hselomein/Car-LED-Controller/CAD/Corey's Rear Enclosure2-Body.stl

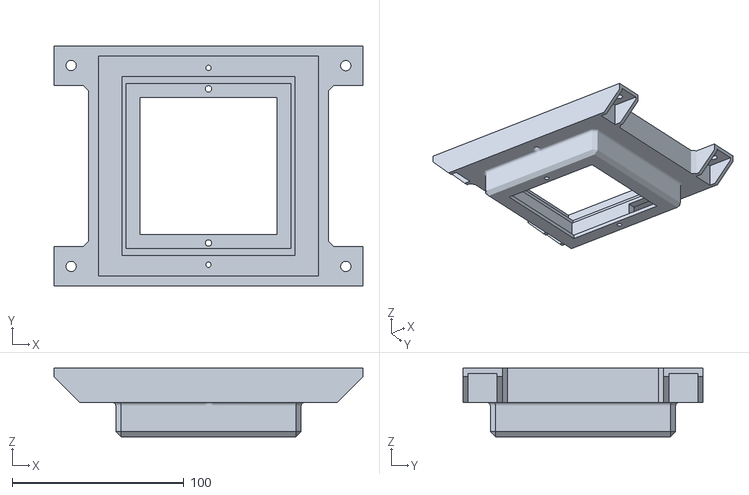
[picture p24: CAD file, 2023-12-11]
CAD/Corey's Rear Enclosure2-Body.stl
180.0 x 140.0 x 40.0
