hselomein/Car-LED-Controller/CAD/Corey's Rear Enclosure2-Door.stl

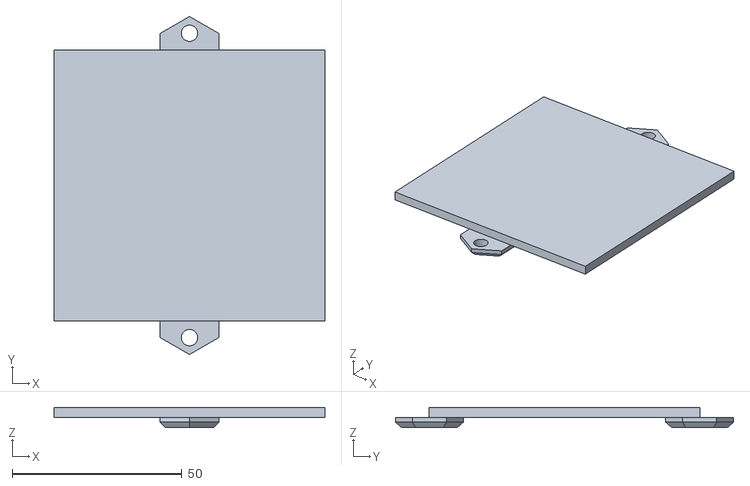
[picture p25: CAD file, 2023-12-05]
CAD/Corey's Rear Enclosure2-Door.stl
79.8 x 99.7 x 6.00
