hselomein/Car-LED-Controller/CAD/Corey's Rear Enclosure-Lid.stl

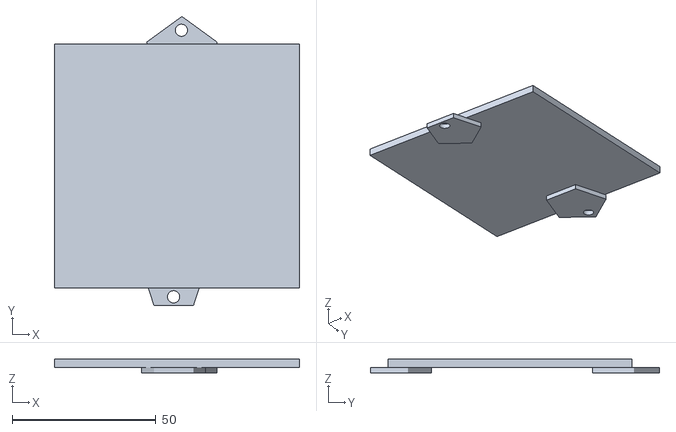
[picture p26: CAD file, 2023-11-26]
CAD/Corey's Rear Enclosure-Lid.stl
85.1 x 100.4 x 5.00
