hselomein/Car-LED-Controller/CAD/GreenyBig.step

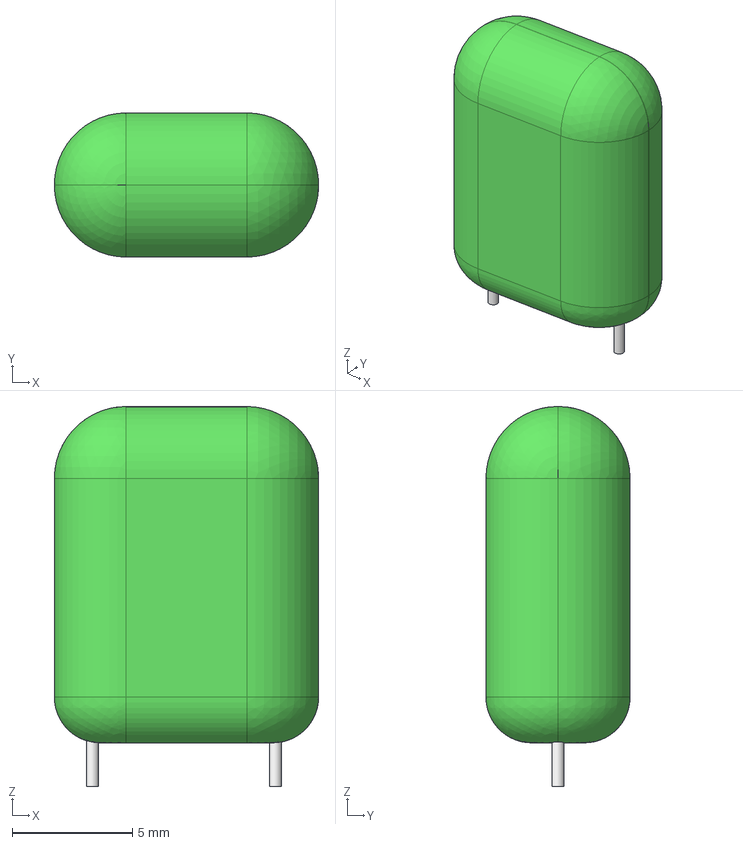
[picture p27: CAD file, 2023-11-26]
CAD/GreenyBig.step
11.0 x 6.00 x 15.8 mm
