hselomein/Car-LED-Controller/CAD/Corey's Rear Enclosure-Body.stl

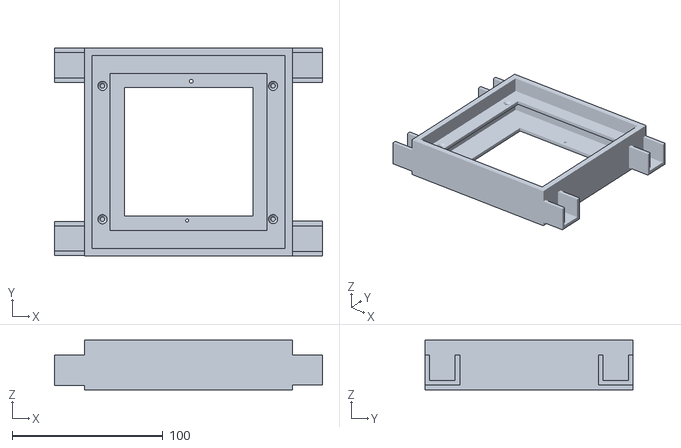
[picture p28: CAD file, 2023-11-26]
CAD/Corey's Rear Enclosure-Body.stl
178.0 x 138.0 x 33.0
