hselomein/Car-LED-Controller/CAD/Corey's Rear Enclosure.FCStd

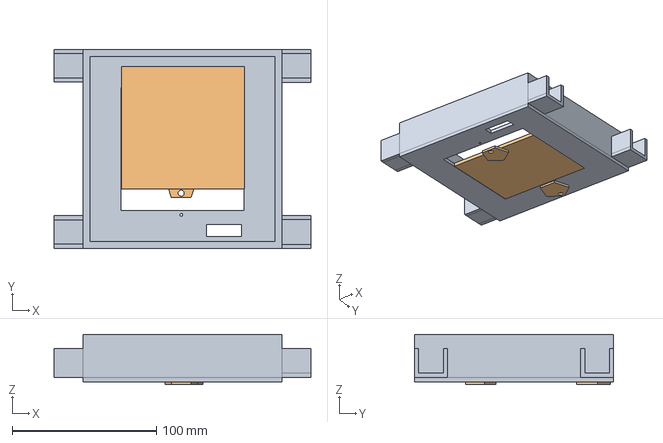
[picture p29: CAD file, 2023-11-26]
CAD/Corey's Rear Enclosure.FCStd
178.0 x 138.0 x 34.9 mm
Lid
