hselomein/Car-LED-Controller/CAD/GreenyMedium.step

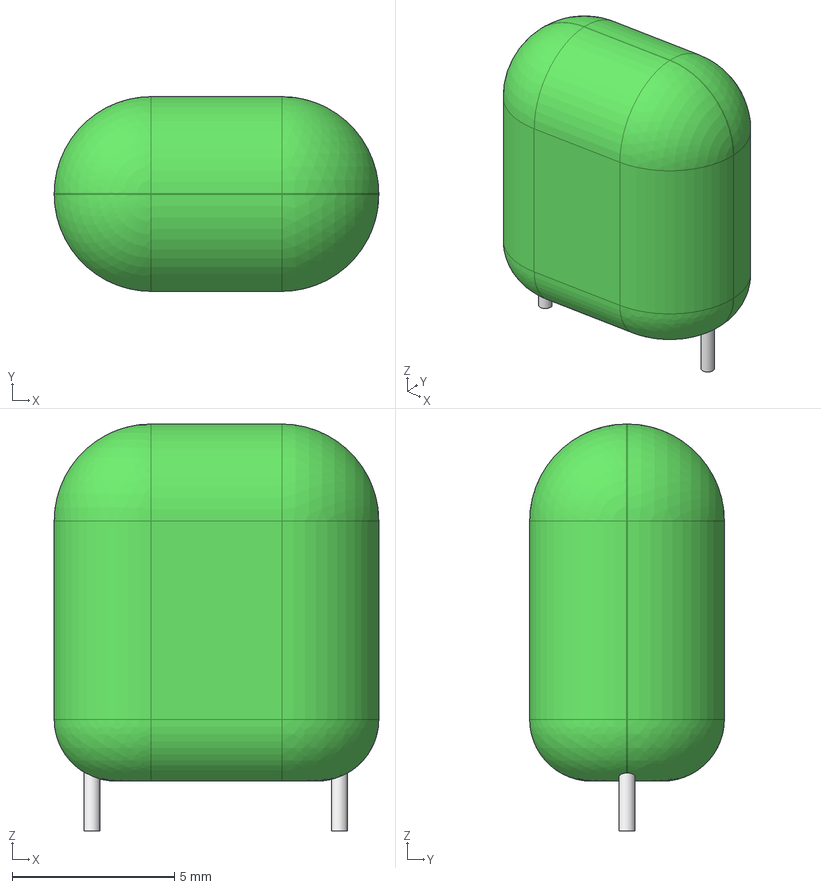
[picture p30: CAD file, 2023-11-26]
CAD/GreenyMedium.step
10.0 x 6.00 x 12.5 mm
