hselomein/Car-LED-Controller/CAD/Corey's Rear Enclosure.20231113-090606.FCStd

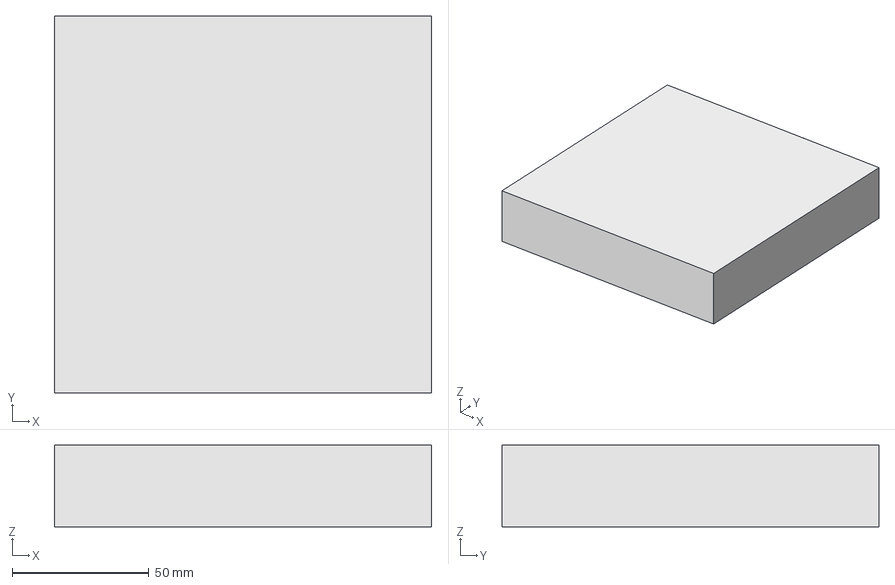
[picture p31: CAD file, 2023-11-26]
CAD/Corey's Rear Enclosure.20231113-090606.FCStd
138.0 x 138.0 x 30.0 mm
