hselomein/Car-LED-Controller/CAD/Controller Enclosure v1-64x64 LED Matrix.stl

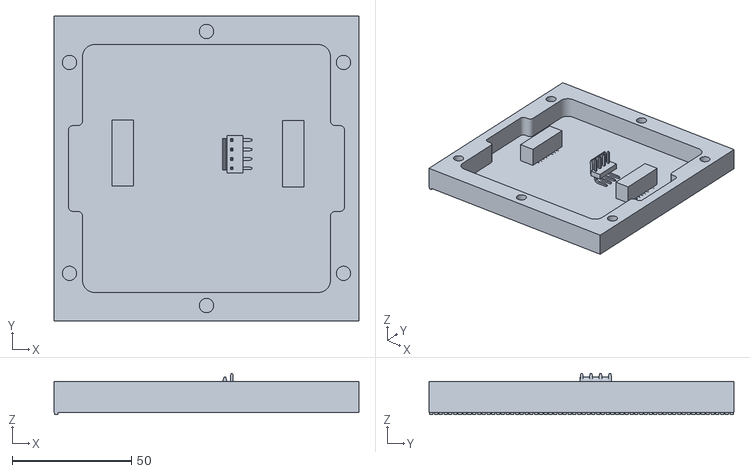
[picture p32: CAD file, 2023-11-26]
CAD/Controller Enclosure v1-64x64 LED Matrix.stl
128.0 x 128.0 x 17.4
