hselomein/Car-LED-Controller/CAD/GreenySmall.step

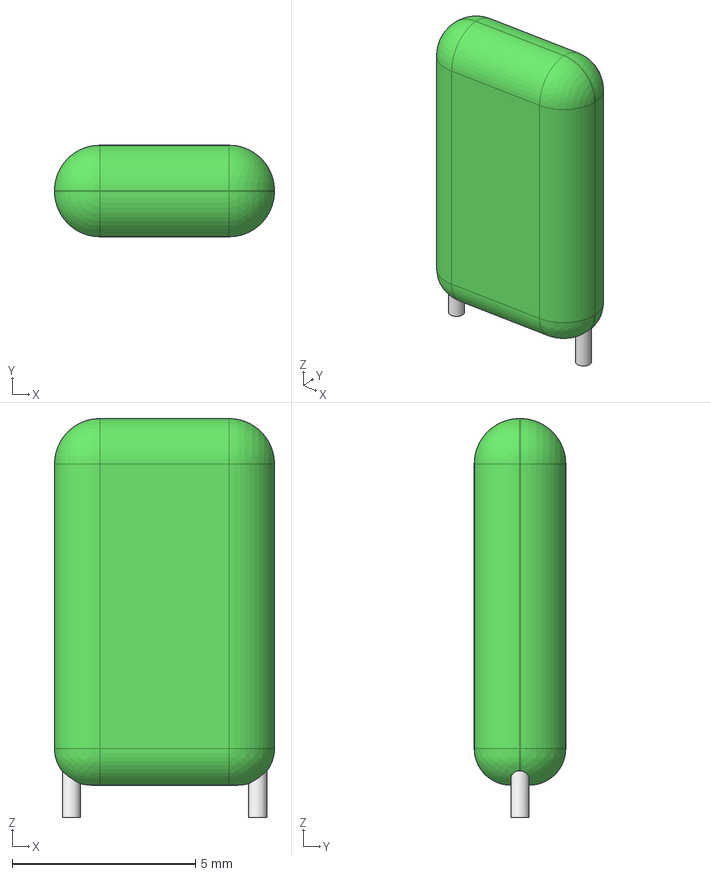
[picture p33: CAD file, 2023-11-26]
CAD/GreenySmall.step
6.00 x 2.50 x 10.9 mm
