hselomein/Car-LED-Controller/CAD/HTST-108-01-L-DV.stp

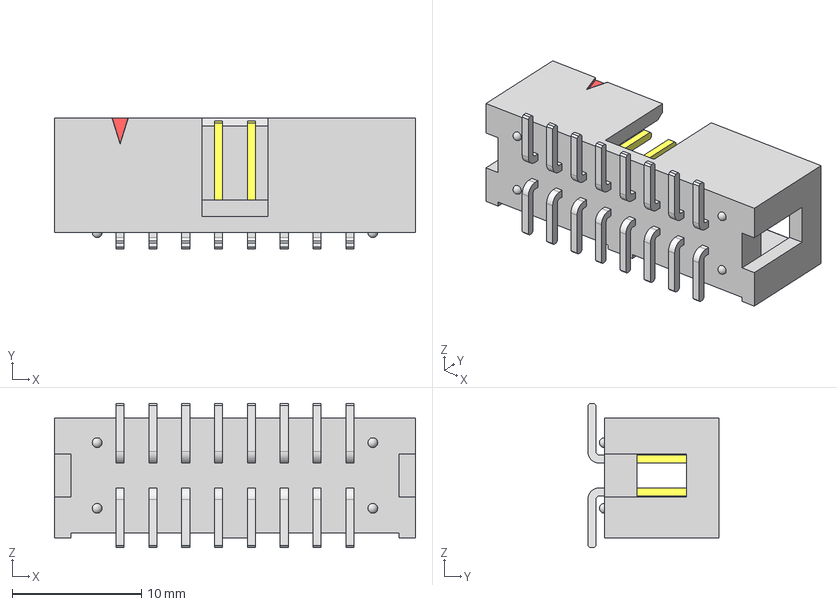
[picture p34: CAD file, 2023-10-11]
CAD/HTST-108-01-L-DV.stp
27.9 x 10.2 x 11.2 mm
T-1S6-08-01-DV-L2_
T-1S6-08-01-DV-L_
HTST-First_Position_Indicator
HTST-108-01-DV_header
