hselomein/Car-LED-Controller/CAD/TSS-113-01-L-D.stp

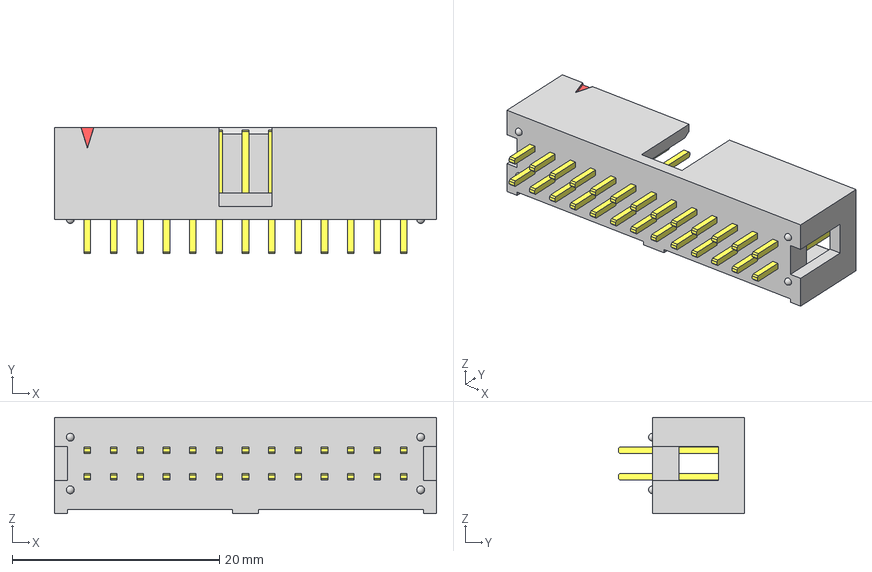
[picture p35: CAD file, 2023-10-11]
CAD/TSS-113-01-L-D.stp
36.8 x 12.2 x 9.27 mm
T-1S6-13-01-D__
TSS-First_Position_Indicator
TSS-113-01-D_header
