hselomein/Car-LED-Controller/CAD/female_header_a-bl254-eg-g19d.stp

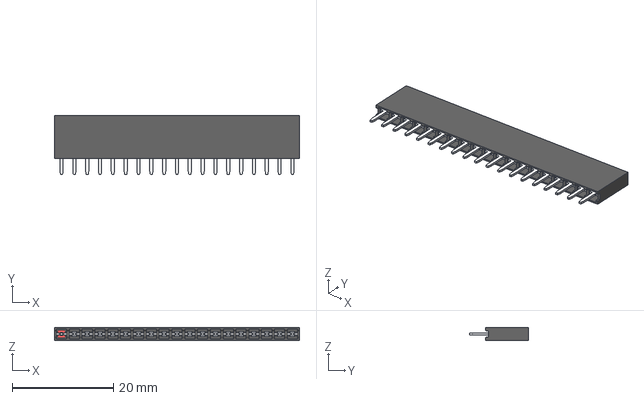
[picture p36: CAD file, 2023-08-22]
CAD/female_header_a-bl254-eg-g19d.stp
48.5 x 11.7 x 2.50 mm
