hselomein/Car-LED-Controller/CAD/female_header_a-bl254-eg-g06d.stp

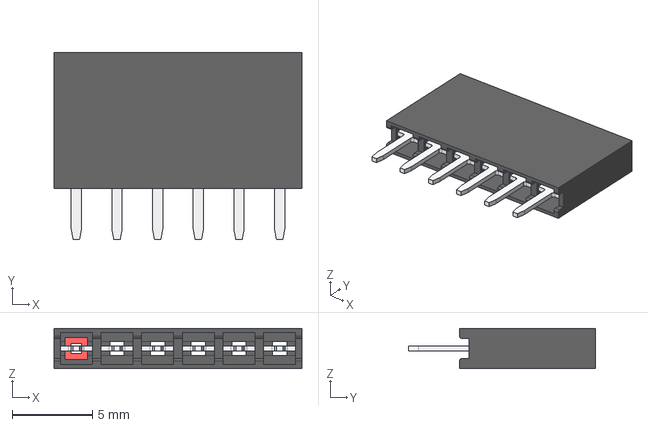
[picture p37: CAD file, 2023-08-22]
CAD/female_header_a-bl254-eg-g06d.stp
15.5 x 11.7 x 2.50 mm
