hselomein/Car-LED-Controller/CAD/pin_header_aw140-eg-g06d.stp

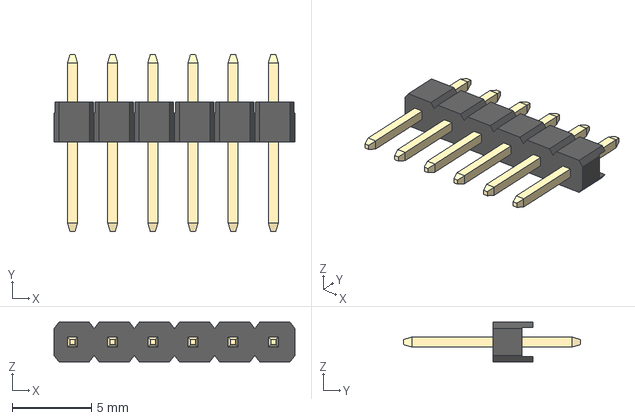
[picture p38: CAD file, 2023-08-22]
CAD/pin_header_aw140-eg-g06d.stp
15.2 x 11.2 x 2.50 mm
