hselomein/Car-LED-Controller/CAD/female_header_a-bl254-eg-g02d.stp

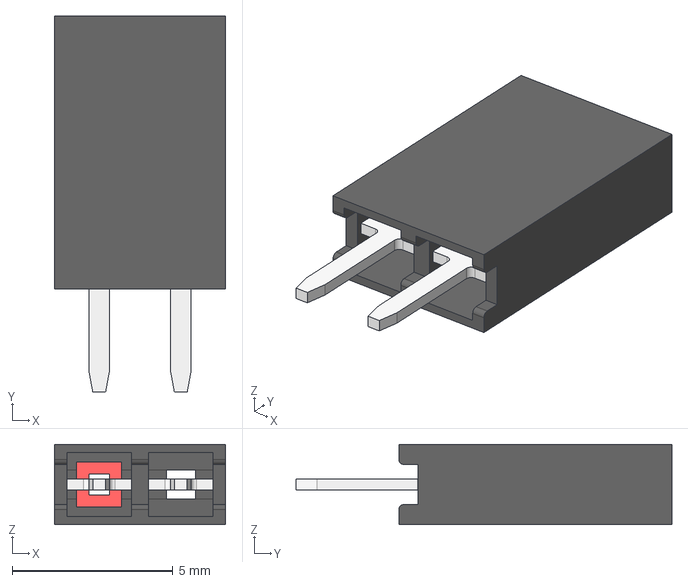
[picture p39: CAD file, 2023-08-22]
CAD/female_header_a-bl254-eg-g02d.stp
5.33 x 11.7 x 2.50 mm
