hselomein/Car-LED-Controller/CAD/Controller Enclosure v1.FCStd

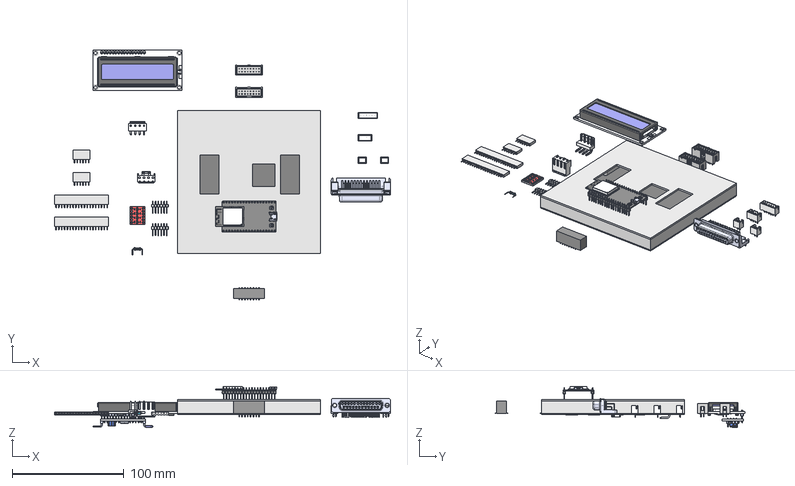
[picture p40: CAD file, 2023-08-22]
CAD/Controller Enclosure v1.FCStd
300.8 x 223.6 x 37.1 mm
Plastic Mount
PCB
board
board001
board002
board003
board004
board005
board006
board007
board008
board009
board010
board011
board012
board013
board014
board015
board016
board017
board018
board019
board020
board021
board022
board023
board024
board025
board026
board027
board028
board029
board030
board031
board032
board033
board034
board035
board036
board037
board038
header
header001
header002
header003
header004
header005
header006
header007
header008
header009
header010
header011
header012
header013
header014
header015
header016
header017
header018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
