hselomein/Car-LED-Controller/CAD/RES_AV_0.25W_100mil_0R_1%.STEP

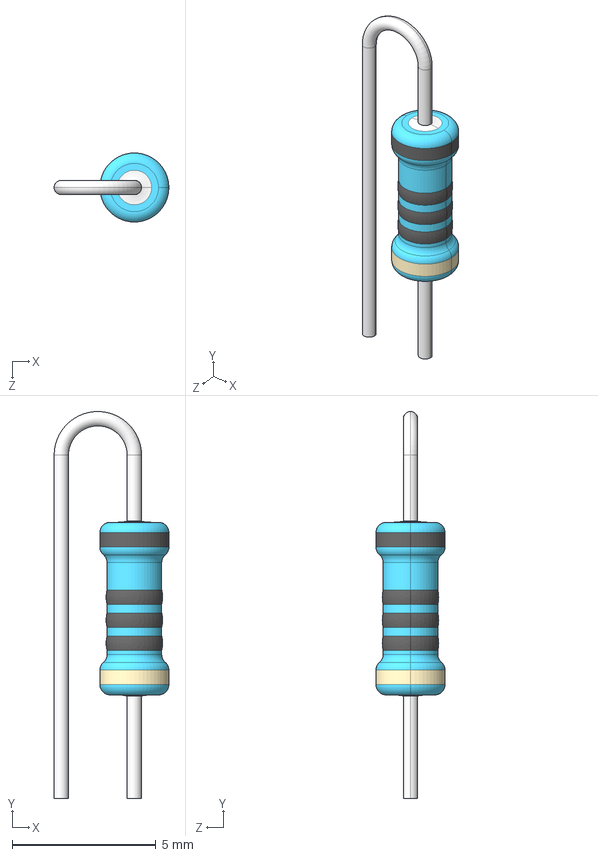
[picture p41: CAD file, 2023-08-22]
CAD/RES_AV_0.25W_100mil_0R_1%.STEP
3.99 x 13.5 x 2.40 mm
