hselomein/Car-LED-Controller/CAD/RES_AH_0.25W_500mil_0R_1%.STEP

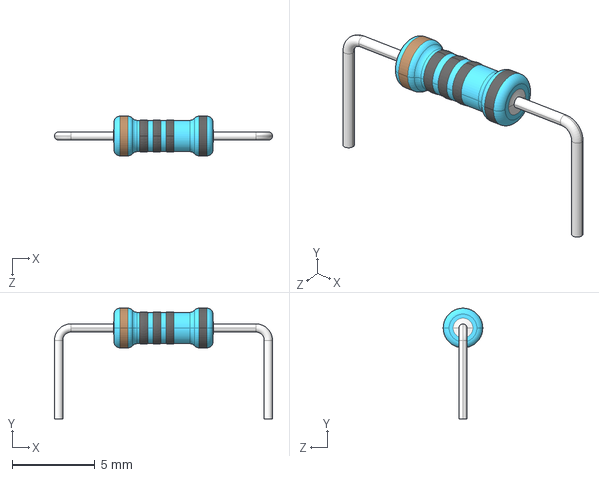
[picture p42: CAD file, 2023-08-22]
CAD/RES_AH_0.25W_500mil_0R_1%.STEP
13.2 x 6.70 x 2.40 mm
