hselomein/Car-LED-Controller/CAD/RES_AV_0.25W_200mil_0R_1%.STEP

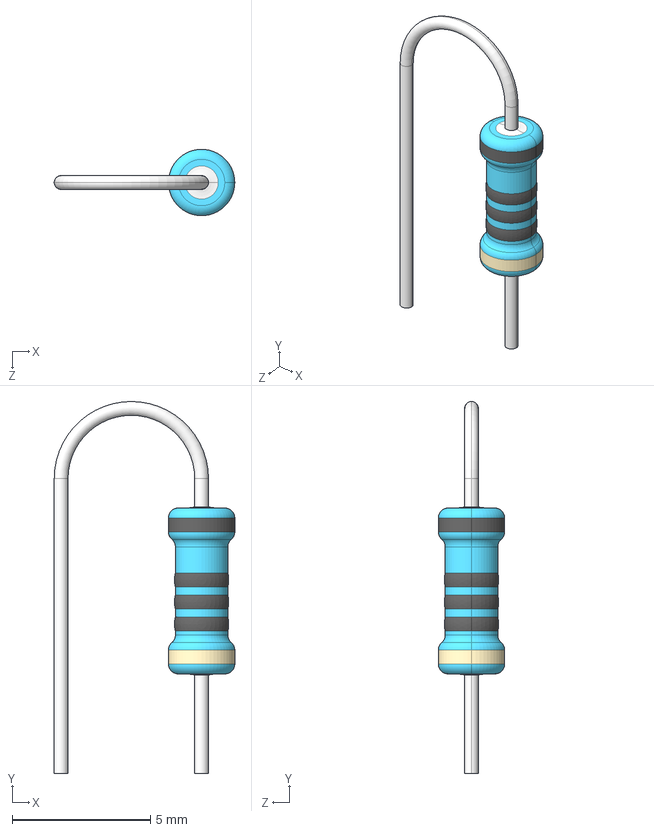
[picture p43: CAD file, 2023-08-22]
CAD/RES_AV_0.25W_200mil_0R_1%.STEP
6.53 x 13.5 x 2.40 mm
