hselomein/Car-LED-Controller/CAD/RES_AV_0.25W_150mil_0R_1%.STEP

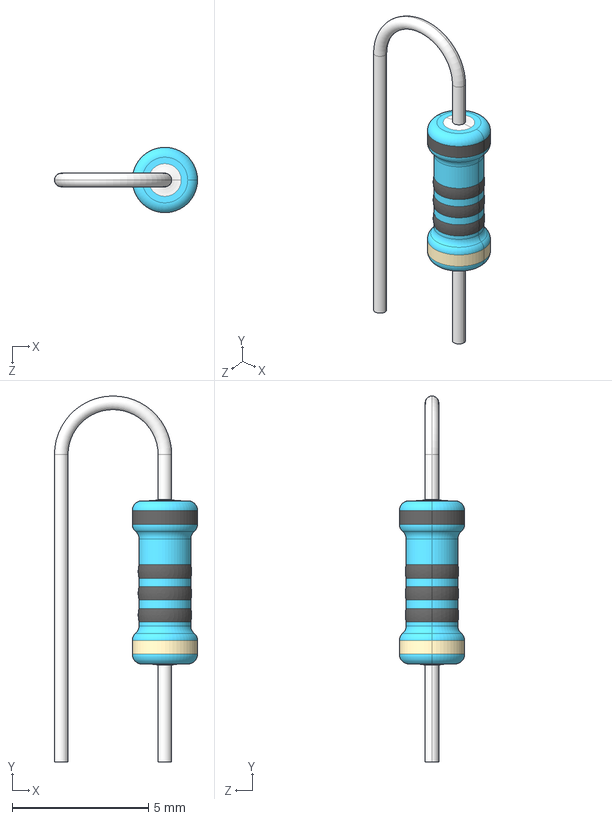
[picture p44: CAD file, 2023-08-22]
CAD/RES_AV_0.25W_150mil_0R_1%.STEP
5.26 x 13.4 x 2.40 mm
