hselomein/Car-LED-Controller/CAD/RES_AH_0.25W_600mil_0R_1%.STEP

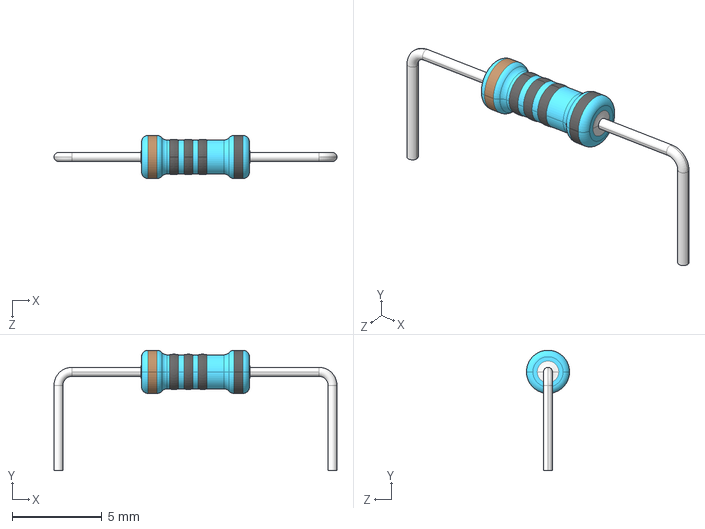
[picture p47: CAD file, 2023-08-22]
CAD/RES_AH_0.25W_600mil_0R_1%.STEP
15.7 x 6.70 x 2.40 mm
