hselomein/Car-LED-Controller/CAD/B4B-XH-A.step

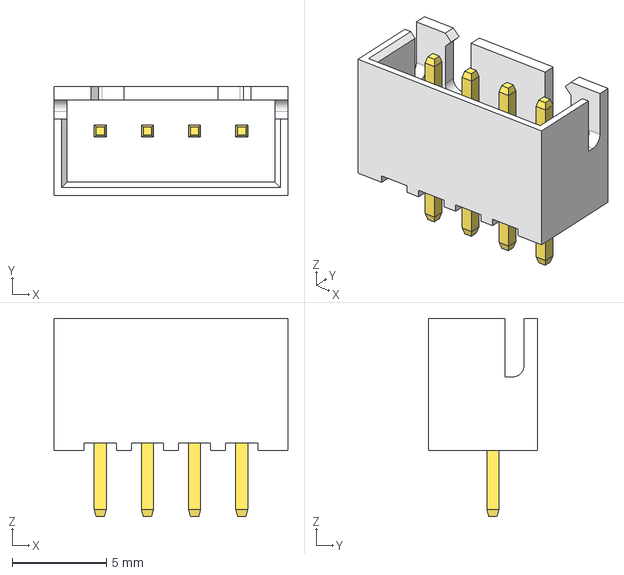
[picture p49: CAD file, 2023-08-22]
CAD/B4B-XH-A.step
12.4 x 5.75 x 10.5 mm
