hselomein/Car-LED-Controller/CAD/B6B-XH-A.step

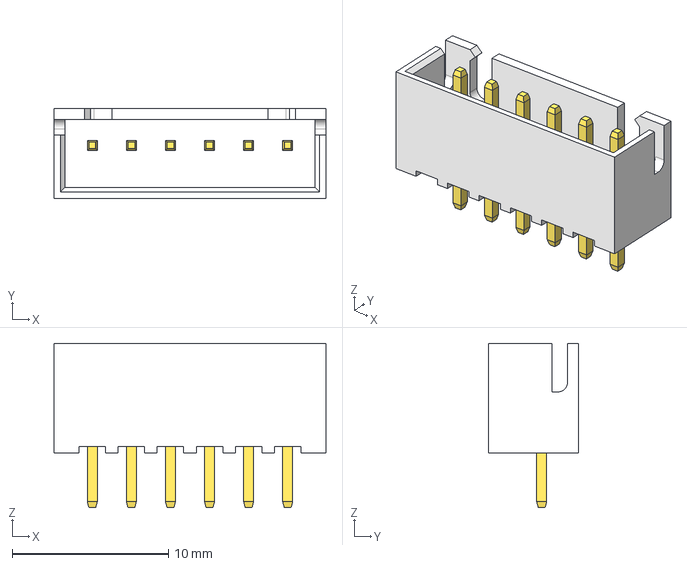
[picture p50: CAD file, 2023-08-22]
CAD/B6B-XH-A.step
17.4 x 5.75 x 10.5 mm
