hselomein/Car-LED-Controller/CAD/B2B-XH-A.step

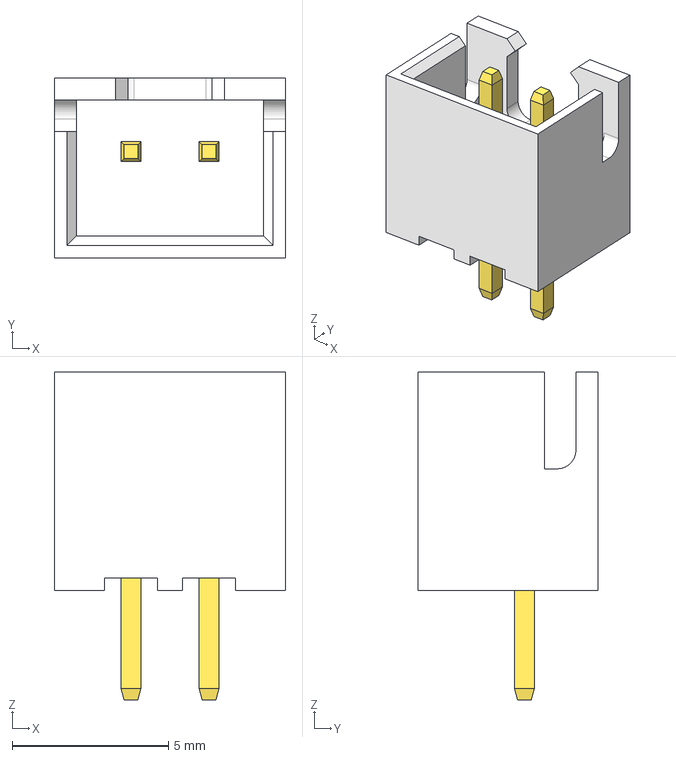
[picture p51: CAD file, 2023-08-22]
CAD/B2B-XH-A.step
7.40 x 5.75 x 10.5 mm
