hselomein/Car-LED-Controller/CAD/DB25S564GTLF--3DModel-STEP-56544.STEP

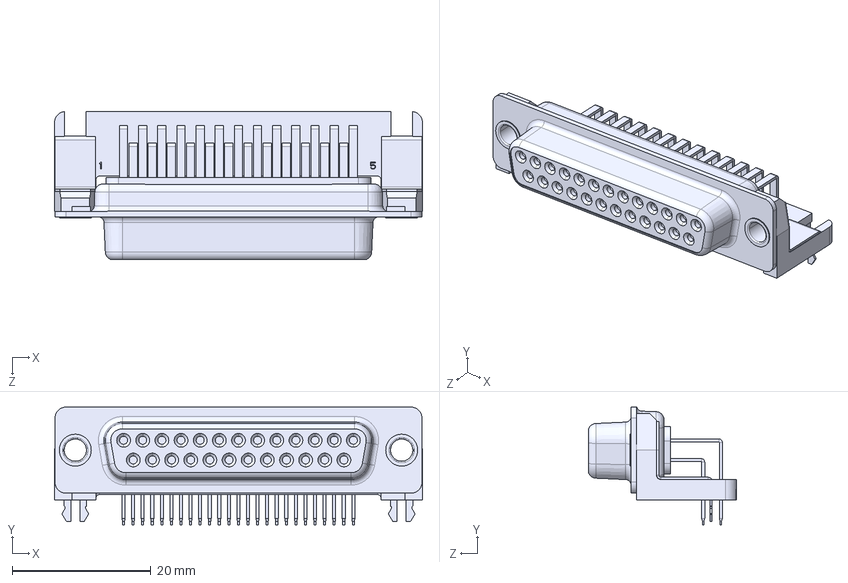
[picture p52: CAD file, 2023-08-21]
CAD/DB25S564GTLF--3DModel-STEP-56544.STEP
53.0 x 17.0 x 21.3 mm
