hselomein/Car-LED-Controller/CAD/SBH11-NBPC-D08-SM-BK.stp

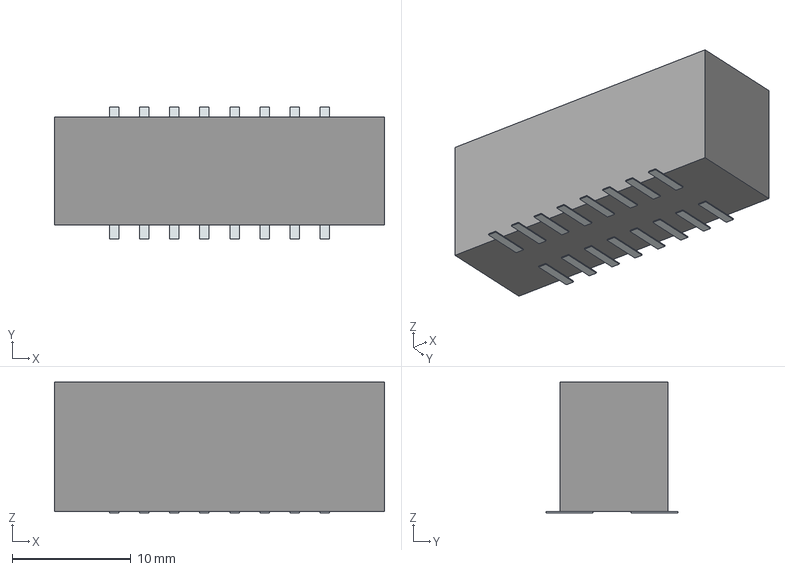
[picture p53: CAD file, 2023-08-21]
CAD/SBH11-NBPC-D08-SM-BK.stp
27.8 x 11.1 x 11.0 mm
Pins
