hselomein/Car-LED-Controller/CAD/TSS-108-01-G-D.stp

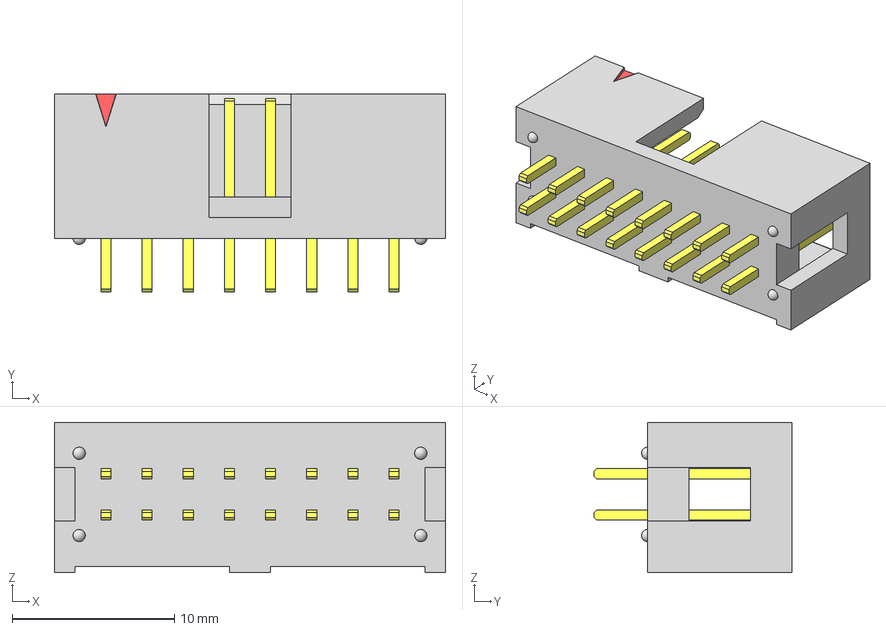
[picture p54: CAD file, 2023-08-21]
CAD/TSS-108-01-G-D.stp
24.1 x 12.2 x 9.27 mm
T-1S6-08-01-D__
TSS-First_Position_Indicator
TSS-108-01-D_header
