hselomein/Car-LED-Controller/CAD/User Library-VHR-4N.step

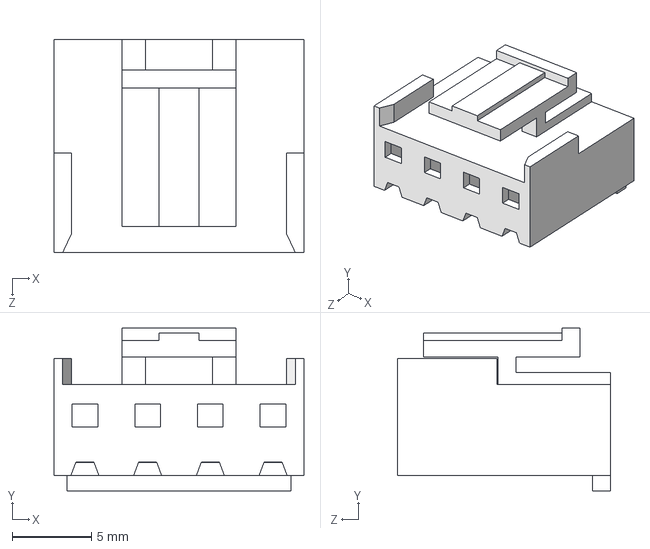
[picture p55: CAD file, 2023-08-21]
CAD/User Library-VHR-4N.step
15.8 x 10.3 x 13.5 mm
