hselomein/Car-LED-Controller/CAD/SFH11-PBPC-D08-ST-BK--3DModel-STEP-56544.STEP

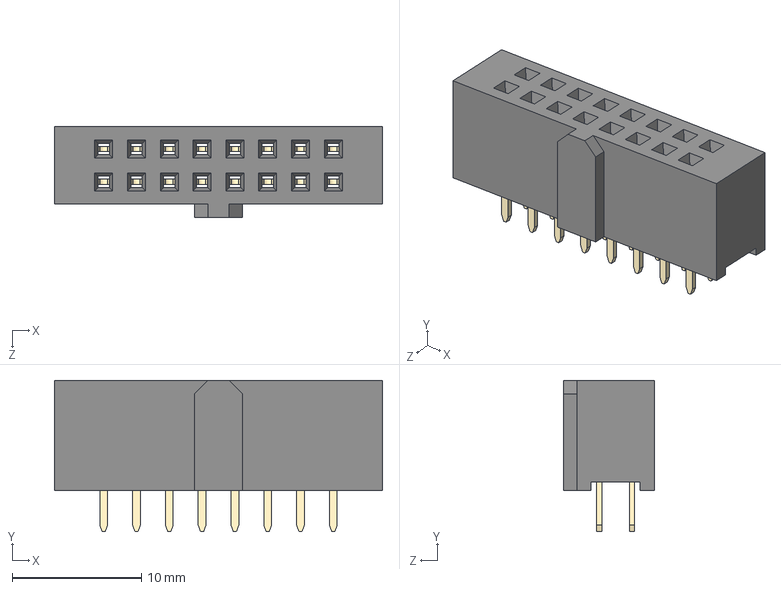
[picture p56: CAD file, 2023-08-21]
CAD/SFH11-PBPC-D08-ST-BK--3DModel-STEP-56544.STEP
25.4 x 11.7 x 7.01 mm
SFH11-xC-Dx-ST-BK body_08
pin^SFH11-xC-Dx-ST-BK Ass x 16
