hselomein/Car-LED-Controller/CAD/User Library-B4PS-VH.STEP

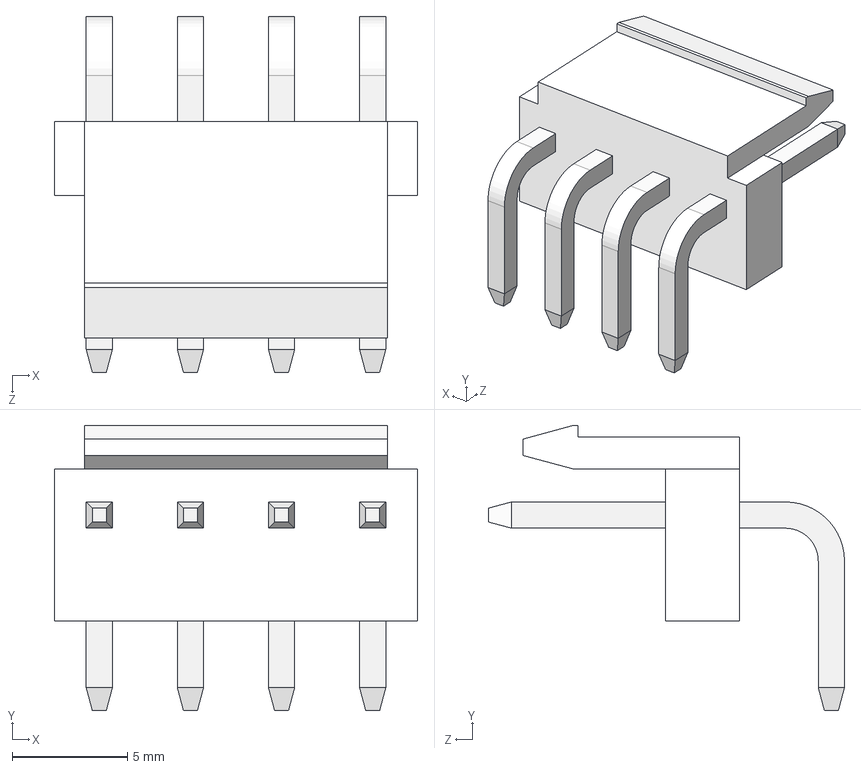
[picture p57: CAD file, 2023-08-21]
CAD/User Library-B4PS-VH.STEP
15.8 x 12.4 x 15.5 mm
User Library-B2P-VH_PinVH_R x 4
User Library-B4P-VH_B4P-body white
