hselomein/Car-LED-Controller/CAD/BOB-12009--3DModel-STEP-1.STEP

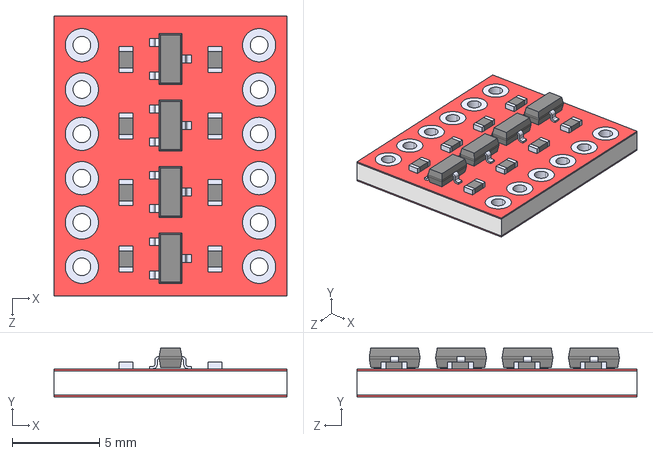
[picture p58: CAD file, 2023-07-23]
CAD/BOB-12009--3DModel-STEP-1.STEP
13.3 x 2.80 x 16.1 mm
