hselomein/Car-LED-Controller/Examples/Emblem-Lyft.c

const uint16_t Emblem-Lyft[41][60] = {
	{57457,57457,57457,57457,57457,57457,57457,57457,57457,57457,57457,57457,57457,57457,57457,57457,57457,57457,57457,57457,57457,57457,57457,57457,57457,57457,57457,57457,57457,57457,57457,57457,57457,57457,57457,57457,57457,57457,57457,57457,57457,57457,57457,57457,57457,57457,57457,57457,57457,57457,57457,57457,57457,57457,57457,57457,57457,57457,57457,57457},
	{57457,57457,57457,57457,57457,57457,57457,57457,57457,57457,57457,57457,57457,57457,57457,57457,57457,57457,57457,57457,57457,57457,57457,57457,57457,57457,57457,57457,57457,57457,57457,57457,57457,57457,57457,57457,57457,57457,57457,57425,57393,57360,57360,57360,57360,57393,57425,57457,57457,57457,57457,57457,57457,57457,57457,57457,57457,57457,57457,57457},
	{57457,57457,57457,57457,57360,57360,57360,57360,57360,57360,57360,57360,57457,57457,57457,57457,57457,57457,57457,57457,57457,57457,57457,57457,57457,57457,57457,57457,57457,57457,57457,57457,57457,57457,57457,57457,57457,57425,57360,57359,59634,60117,60311,60311,60085,57522,57359,57360,57425,57457,57457,57457,57457,57457,57457,57457,57457,57457,57457,57457},
	{57457,57457,57457,57360,65342,65374,65342,65342,65342,65342,65342,65535,57360,57457,57457,57457,57457,57457,57457,57457,57457,57457,57457,57457,57457,57457,57457,57457,57457,57457,57457,57457,57457,57457,57457,57457,57360,57360,62423,65535,65535,65535,65535,65535,65535,65535,65470,60279,57359,57393,57457,57457,57457,57457,57457,57457,57457,57457,57457,57457},
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

};
